rxiliv/admAIre/hardware/pcb/admaire-electrical_schematic.kicad_sch

## KiCad design hardware/pcb/admaire-electrical_schematic.kicad_sch (2026-09-15)

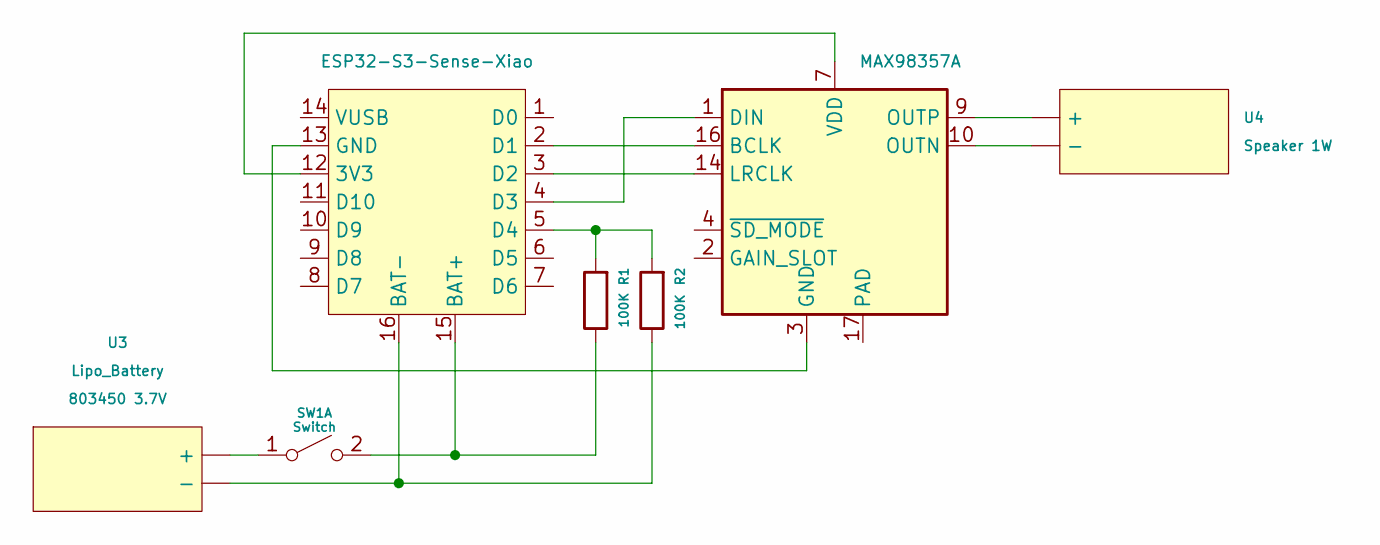
[picture p7: schematic admaire-electrical_schematic.kicad_sch]

Parts:
R1, R2: 100K
SW1: Switch
U1: ESP32-S3-Sense-Xiao
U2: MAX98357A; TQFN-16-1EP_3x3mm_P0.5mm_EP1.23x1.23mm
U3: Lipo_Battery
U4: Speaker 1W

Connections:
unnamed: R1.1, SW1.2 (B), U1.15 (BAT+)
unnamed: R1.2, R2.2, U1.5 (D4)
unnamed: R2.1, U1.16 (BAT-), U3.
unnamed: SW1.1 (A), U3.
unnamed: U1.2 (D1), U2.16 (BCLK)
unnamed: U1.3 (D2), U2.14 (LRCLK)
unnamed: U1.4 (D3), U2.1 (DIN)
unnamed: U1.12 (3V3), U2.7 (VDD), U2.8 (VDD)
unnamed: U1.13 (GND), U2.3 (GND), U2.11 (GND), U2.15 (GND)
unnamed: U2.9 (OUTP), U4.
unnamed: U2.10 (OUTN), U4.
